ETML-ES-SLO/PRJ_2113_D-sElectronique/doc/Schéma bloc.docx

SPI / CONFIG

3.3V

INT1

3.3V

Maintien d’alimentation

Microcontrôleur

3.3V

V pile

Alimentation

Accéléromètre

Régulateur / élévateur
