ETML-ES-SLO/PRJ_2113_D-sElectronique/doc/PV/PV_N2_MaximeColloud_14_10_2021.docx

Procès-verbal du 14.10.2021

Présents

- M. Serge Castoldi
- M. Maxime Colloud

État des lieux

- Schéma et PCB presque terminé (modifications à faire)
- Composants presque choisi (changements à faire)

Problèmes rencontrés

- Self sous dimensionnée
- Reconfiguration de l’accéléromètre non présente si pile retirée ou vide

Solutions proposées

- Ajout d’un bouton pour reconfigurer l’accéléromètre en cas de pile retirée ou vide

Décisions prises

- Changement inductance L1 et C1
- Ajout du signal interrupt sur le microcontrôleur
- Modification de la taille du PCB avec une largeur plus grande que spécifié dans le cahier des

Charge pour une simplification du boitier et hauteur plus petite

Suite du projet / objectifs - jusqu’au jeudi 21.10.2021

- Modifier le schéma, PCB
- Créer un boitier
- Tester avec le kit micro MM la configuration d’un chip MM
- Commander le PCB et composants

Prochaine réunion:

21.10.2021 à 13h

Destinataires de ce PV

- Grégoire Rossier → Doyen ES
- Serge Castoldi → Enseignant ES

Lausanne le 14.10.2021

Maxime Colloud

PV_N2_MaximeColloud_14_10_2021.docx 14.10.2021 - page 2 / 2

Ecole supérieure, école des métiers Lausanne Version 2.2 Rue de Sébeillon 12 du 02.09.2021 CH-1004 Lausanne www.etml-es.ch PV_N2_MaximeColloud_14_10_2021.docx | 1 / 2 |

ETML-ES PV de séance diplôme
