ETML-ES-SLO/PRJ_2113_D-sElectronique/doc/PDF/2113_Suivi d'avancement.pdf

## Projet 2113 Dé électronique Maxime Colloud

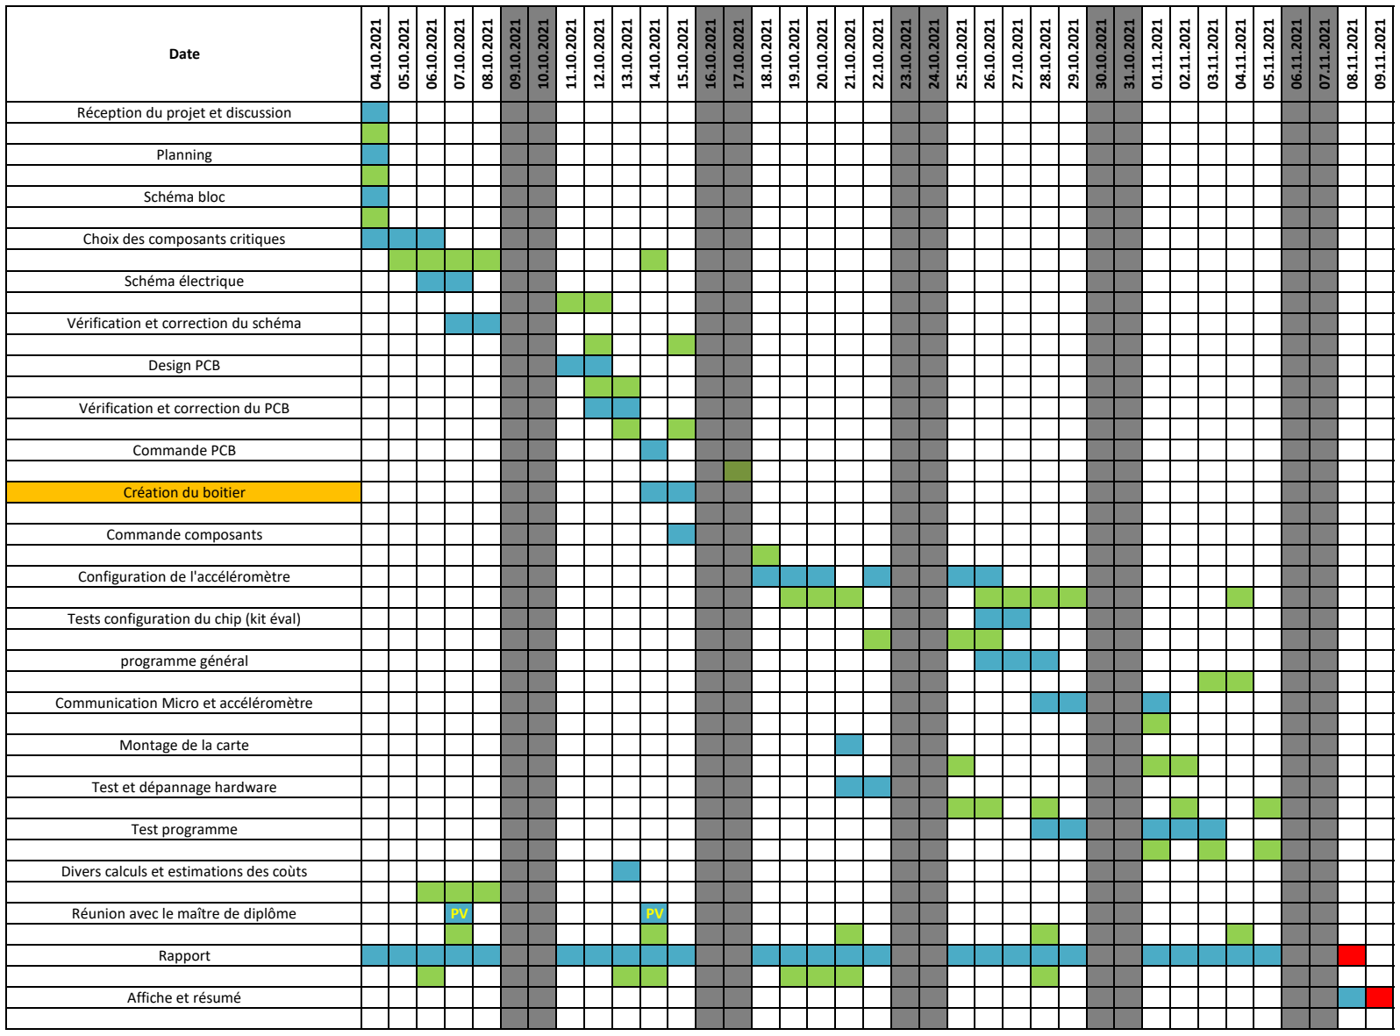
[picture p47: figure]
Réception du projet et discussion; Planning; Schéma bloc; Choix des composants critiques; Schéma électrique; Vérification et correction du schéma; Design PCB; Vérification et correction du PCB; Commande PCB; Création du boitier; Commande composants; Configuration de l'accéléromètre; Tests configuration du chip (kit éval); programme général; Communication Micro et accéléromètre; Montage de la carte; Test et dépannage hardware; Test programme; Divers calculs et estimations des coùts; Réunion avec le maître de diplôme; Rapport; Affiche et résumé; Date

# : deadline du projet ⁰⁸.10.2021 09.10.2021
