ETML-ES-SLO/PRJ_2113_D-sElectronique/doc/PDF/DeElectroniqueC.pdf

1 #include "DeElectronique.h" 2

### 3 void NONUM (void)

4 {
5 LED0 = 0;
6 LED1 = 0;
7 LED2 = 0;
8 LED3 = 0;
9 LED4 = 0;
10 LED5 = 0;
11 LED6 = 0;
12 }

### 13 void NUM1 (void)

14 {
15 LED3 = 1;
16 }

### 17 void NUM2 (void)

18 {
19 LED0 = 1;
20 LED6 = 1;
21 }

### 22 void NUM3 (void)

23 {
24 LED0 = 1;
25 LED3 = 1;
26 LED6 = 1;
27 }

### 28 void NUM4 (void)

29 {
30 LED0 = 1;
31 LED2 = 1;
32 LED4 = 1;
33 LED6 = 1;
34 }

### 35 void NUM5 (void)

36 {
37 LED0 = 1;
38 LED2 = 1;
39 LED3 = 1;
40 LED4 = 1;
41 LED6 = 1;
42 }

### 43 void NUM6 (void)

44 {
45 LED0 = 1;
46 LED1 = 1;
47 LED2 = 1;
48 LED4 = 1;
49 LED5 = 1;
50 LED6 = 1;
51 }
52

### 53 void RandomNum (int Number)

54 {
55 uint8_t EntierNumber;
56
57 EntierNumber = Number %6; 58

### 59 switch (EntierNumber)

60 {

### 61 case 0 :

62 NUM1();
63 break;

### 64 case 1 :

65 NUM2();
66 break;

### 67 case 2 :

68 NUM3();
69 break;

### 70 case 3 :

71 NUM4();
72 break;

### 73 case 4 :

74 NUM5();
75 break | ;
76 case | 5 :
77 NUM6();
78 break | ;
79 default | :
80 break | ;
81 | }
82 | }
