ETML-ES-SLO/PRJ_2113_D-sElectronique/doc/PDF/DeElectroniqueH.pdf

1 /*
2 | * File: | DeElectronique.h
3 * Author: maxcolloud
4 *
5 * Created on November 3, 2021, 1:35 PM 6 */
7
8 #include "xc.h"
9 #include "Accelerometre.h" 10
11 #ifndef DEELECTRONIQUE_H 12 #define DEELECTRONIQUE_H 13
14
15 #ifdef __cplusplus

### 16 extern "C" {

17 #endif
18
19 #define INT_SHAKE PORTBbits.RB12 20
21 #define LED0 LATAbits.LATA0
22 #define LED1 LATAbits.LATA1
23 #define LED2 LATAbits.LATA2 24 #define LED3 LATBbits.LATB2 25 #define LED4 LATAbits.LATA3 26 #define LED5 LATBbits.LATB4 27 #define LED6 LATAbits.LATA4 28
29 #define HOLD LATBbits.LATB13 30
31 // Fonctions
32 void NONUM (void);
33 void NUM1 (void);
34 void NUM2 (void);
35 void NUM3 (void);
36 void NUM4 (void);
37 void NUM5 (void);
38 void NUM6 (void);
39 void RandomNum (int Number); 40
41 #ifdef __cplusplus
42 }
43 #endif
44
45 #endif /* DEELECTRONIQUE_H */ 46
47
