ETML-ES-SLO/PRJ_2113_D-sElectronique/doc/PDF/Planning.pdf

## Projet 2113 Dé électronique Maxime Colloud

10.10.2021

11.10.2021

12.10.2021

13.10.2021

14.10.2021

15.10.2021

16.10.2021

17.10.2021

18.10.2021

19.10.2021

20.10.2021

21.10.2021

22.10.2021

23.10.2021

24.10.2021

25.10.2021

26.10.2021

27.10.2021

28.10.2021
29.10.2021

30.10.2021

31.10.2021

01.11.2021

02.11.2021

03.11.2021

04.11.2021

05.11.2021

06.11.2021

07.11.2021

08.11.2021

09.11.2021

Date

Réception du projet et discussion Planning
Schéma bloc
Choix des composants critiques Schéma électrique
Vérification et correction du schéma | : deadline du projet ⁰⁸.10.2021 | | 09.10.2021

Design PCB
Vérification et correction du PCB Commande PCB
Création du boitier
Commande composants
Configuration de l'accéléromètre Tests configuration du chip (kit éval) programme général
Communication Micro et accéléromètre Montage de la carte
Test et dépannage hardware
Test programme
Divers calculs et estimations des coùts
Réunion avec le maître de diplôme | | PV | | PV
Rapport
Affiche et résumé

04.10.2021

05.10.2021

06.10.2021

07.10.2021
