ETML-ES-SLO/PRJ_2113_D-sElectronique/doc/PDF/PV_N1_MaximeColloud_07_10_2021.pdf

ETML⁻ES
PV de séance | diplôme
Ecole supérieure, école des métiers Lausanne | Version 2.2
Rue de Sébeillon 12 | du 02.09.2021
CH-1004 Lausanne | www.etml-es.ch
Procès verbal TYPE_v2-2.docx | | 1 / 2 |

## Procès-verbal du 07.10.2021

Présents

- M. Sege Castoldi
- M. Maxime Colloud

État des lieux

- Choix d’une variante de montage (PIC32MM, 1 pile alkaline, 1 convertisseur step-up)

Problèmes rencontrés

- Disponibilité des composants faible
- Step-up présélectionné non adapté aux faibles consommations.

Solutions proposées

- Ajout d’un système de sécurité d’alimentation inverse

Décisions prises

- Utilisation du PICMM 20 pin
- utilisation de l’accéléromètre MC3419
- choix d’un convertisseur step-up en basse consommation.
- Utilisation d’un mosfet canal-p pour la protection d’alimentation inverse

Suite du projet / objectifs - jusqu’au jeudi 14 août

- Choix des derniers composants, Schéma, Design PCB.

Prochaine réunion:

14.10.2021 à 13h

ETML⁻ES

Procès verbal TYPE_v2-2.docx | 07.10.2021 - page 2 / 2

Destinataires de ce PV

- Grégoire Rossier → Doyen ES
- Serge Castoldi → Enseignant ES

Lausanne le 07.10.2021

Maxime Colloud
