ETML-ES-SLO/PRJ_2113_D-sElectronique/doc/PDF/PV_N3_MaximeColloud_21_10_2021.pdf

ETML⁻ES
PV de séance | diplôme
Ecole supérieure, école des métiers Lausanne | Version 2.2
Rue de Sébeillon 12 | du 02.09.2021
CH-1004 Lausanne | www.etml-es.ch
PV_N2_MaximeColloud_21_10_2021.docx | | 1 / 2 |

## Procès-verbal du 21.10.2021

Présents

- M. Serge Castoldi
- M. Maxime Colloud

État des lieux

- PCB commandé et reçu
- Composants reçu
- Premier de configuration pic32MM fait sur le kitMM

Problèmes rencontrés

- Aucun

Solutions proposées

- Le cahier des charges stipule que le chiffre doit être affiché quand le dé est reposé à l’horizontal. N’étant pas pratique pour l’utilisateur, il faudrait modifier pour afficher lors d’un arrêt de mouvement.

Décisions prises

- Afficher le chiffre lors d’un arrêt de mouvement.

Suite du projet / objectifs - jusqu’au jeudi 21.10.2021

- Montage PCB
- Programmation

Prochaine réunion:

28.10.2021 à 13h

ETML⁻ES

PV_N2_MaximeColloud_21_10_2021.docx | 25.10.2021 - page 2 / 2

Destinataires de ce PV

- Grégoire Rossier → Doyen ES
- Serge Castoldi → Enseignant ES

Lausanne le 25.10.2021

Maxime Colloud
