ETML-ES-SLO/PRJ_2113_D-sElectronique/doc/Affiche PROJET SLO_v1.pdf

Maxime Colloud
TECHNICIEN-NE ES EN GÉNIE ÉLECTRIQUE / 2020-2021

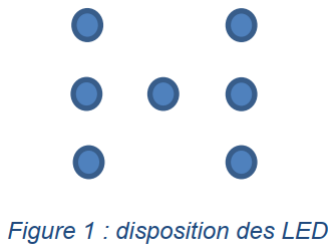
[picture p51: figure]

### www.etml-es.ch

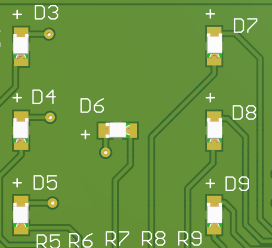
[picture p52: figure]
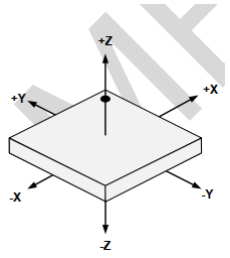
[picture p53: figure]

rue de Sébeillon 12, 1004 Lausanne | ETML

DeElectronique

Le dé peut détecter les actions de secouement et se réveiller par cette même action. Par problème de dimensionnement de l’élévateur, le dé ne fonctionne pas à l’utilisation d’une pile. En debug, il peut générer un chiffre aléatoire lors d’un secouement détecté.

Ce projet est un dé électronique destiné à être distribué aux visiteurs des portes ouvertes de l’ES. Le dé a pour objectif d’afficher un chiffre lorsqu’il détecte une action de secouement. Le chiffre s’affichera pour une durée de 10sec. L’appareil utilise une pile AA pour son fonctionnement et possède une grande autonomie.

## Affichage des chiffres sous la forme d’un dé à lancer

## Fonctionnement par une pile AA. Simple d’utilisation et avec une bonne autonomie
