ETML-ES-SLO/PRJ_2113_D-sElectronique/doc/PDF/mainc.pdf

1 /**

### 2 Generated main.c file from MPLAB Code Configurator

3
4 @Company
5 Microchip Technology Inc.
6
7 @File Name

### 8 main.c

9
10 @Summary
11 This is the generated main.c using PIC24 / dsPIC33 / PIC32MM MCUs.
12
13 @Description

### 14 This source file provides main entry point for system intialization and

application code development.

### 15 Generation Information : 16 Product Revision : PIC24 / dsPIC33 / PIC32MM MCUs - 1.75.1

17 | Device | : PIC32MM0064GPL020

### 18 The generated drivers are tested against the following:

19 | Compiler | : XC16 v1.35
20 | MPLAB | : MPLAB X v5.05
21 */
22
23 /*
24 (c) 2016 Microchip Technology Inc. and its subsidiaries. You may use this 25 software and any derivatives exclusively with Microchip products.
26

27 THIS SOFTWARE IS SUPPLIED BY MICROCHIP "AS IS". NO WARRANTIES, WHETHER 28 EXPRESS, IMPLIED OR STATUTORY, APPLY TO THIS SOFTWARE, INCLUDING ANY IMPLIED 29 WARRANTIES OF NON-INFRINGEMENT, MERCHANTABILITY, AND FITNESS FOR A 30 PARTICULAR PURPOSE, OR ITS INTERACTION WITH MICROCHIP PRODUCTS, COMBINATION

31 WITH ANY OTHER PRODUCTS, OR USE IN ANY APPLICATION.
32
33 IN NO EVENT WILL MICROCHIP BE LIABLE FOR ANY INDIRECT, SPECIAL, PUNITIVE,

34 INCIDENTAL OR CONSEQUENTIAL LOSS, DAMAGE, COST OR EXPENSE OF ANY KIND 35 WHATSOEVER RELATED TO THE SOFTWARE, HOWEVER CAUSED, EVEN IF MICROCHIP HAS 36 BEEN ADVISED OF THE POSSIBILITY OR THE DAMAGES ARE FORESEEABLE. TO THE 37 FULLEST EXTENT ALLOWED BY LAW, MICROCHIP'S TOTAL LIABILITY ON ALL CLAIMS IN

38 ANY WAY RELATED TO THIS SOFTWARE WILL NOT EXCEED THE AMOUNT OF FEES, IF ANY, 39 THAT YOU HAVE PAID DIRECTLY TO MICROCHIP FOR THIS SOFTWARE.
40

### 41 MICROCHIP PROVIDES THIS SOFTWARE CONDITIONALLY UPON YOUR ACCEPTANCE OF THESE

42 TERMS.
43 */
44
45 /**

### 46 Section: Included Files

47 */
48
49 #include "mcc_generated_files/system.h"
50 #include "mcc_generated_files/spi1.h"
51 #include "mcc_generated_files/pin_manager.h" 52 #include "Accelerometre.h"
53 #include "DeElectronique.h"
54 #include "mcc_generated_files/tmr1.h"
55 /*

### 56 Main application

57 */

### 58 int main(void)

59 {
60 // initialize the device
61 SYSTEM_Initialize();
62 | HOLD = 1; | //assure maintien alim.
63
64 MC3419_start();
65
66 | // | if (!INT_SHAKE)
67 | // | {
68 | // | MC3419_start();
69 | // | HOLD = 0;
70 | // | while(1);
71 | // | }
72 | // | uint8_t test;

73 | // int seed;
74 while (1)
75 {
76 | // test = MC3419_ReadStatusRegister();
77 | // if (test == SHAKE_INT)
78 | // {
79 | // seed = ReadRegister8(addr_Xout_Ex_L);
80 | // seed = seed + ReadRegister8(addr_Xout_Ex_H);
81 | // seed = seed + ReadRegister8(addr_Yout_Ex_L);
82 | // seed = seed + ReadRegister8(addr_Yout_Ex_H);
83 | // seed = seed + ReadRegister8(addr_Zout_Ex_L);
84 | // seed = seed + ReadRegister8(addr_Zout_Ex_H);
85 | // srand (seed);
86 | // seed = rand();
87 | // RandomNum (seed);
88 TMR1_Start();
89 | // }
90 }
91 return 1;
92 }
93 /**
94 End of File
95 */
