ETML-ES-SLO/PRJ_2113_D-sElectronique/soft/2113_DeElectronique_V2.X/latex/main_8c__incl.pdf

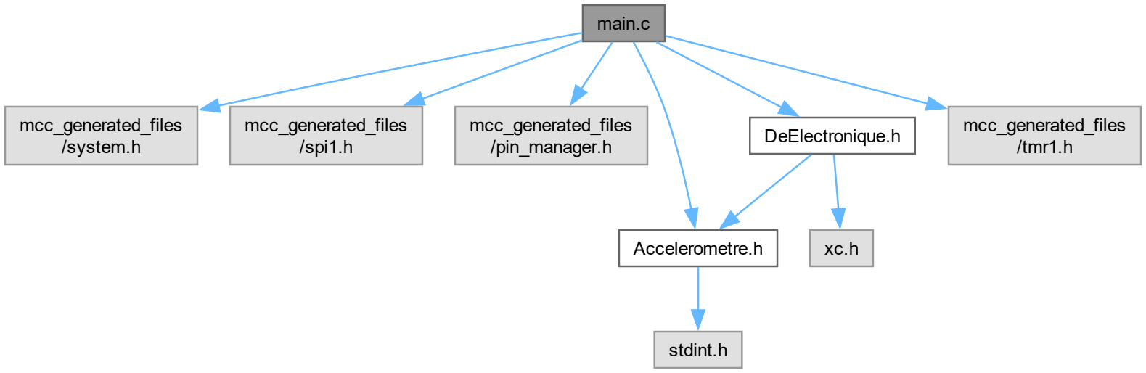
[picture p54: figure]
main.c; mcc_generated_files /system.h; mcc_generated_files /spi1.h; mcc_generated_files /pin_manager.h; Accelerometre.h; DeElectronique.h; mcc_generated_files; /tmr1.h; stdint.h
