ETML-ES-SLO/PRJ_2113_D-sElectronique/soft/2113_DeElectronique_V3.X/code2flow/soft_v3.png

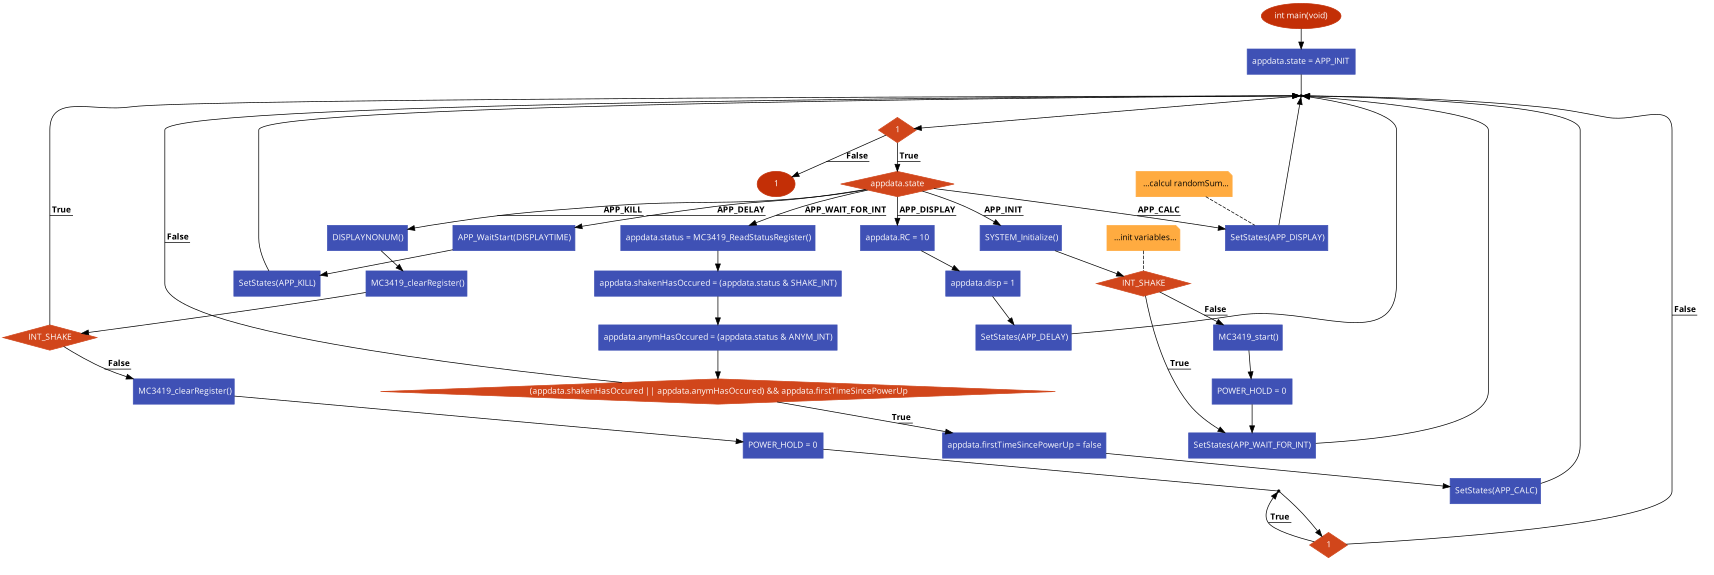
soft/2113_DeElectronique_V3.X/code2flow/soft_v3.png
