ETML-ES-SLO/PRJ_2113_D-sElectronique/soft/2113_DeElectronique_V3.X/code2flow/State_Delay.png

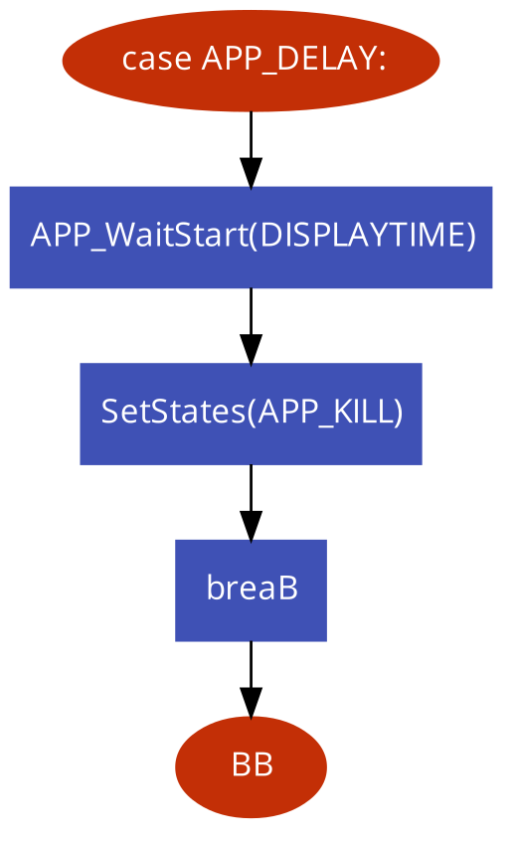
soft/2113_DeElectronique_V3.X/code2flow/State_Delay.png
