ETML-ES-SLO/PRJ_2113_D-sElectronique/soft/2113_DeElectronique_V3.X/html/_accelerometre_8c_a3add481cd74b85a6100f501bc62df540_cgraph.png

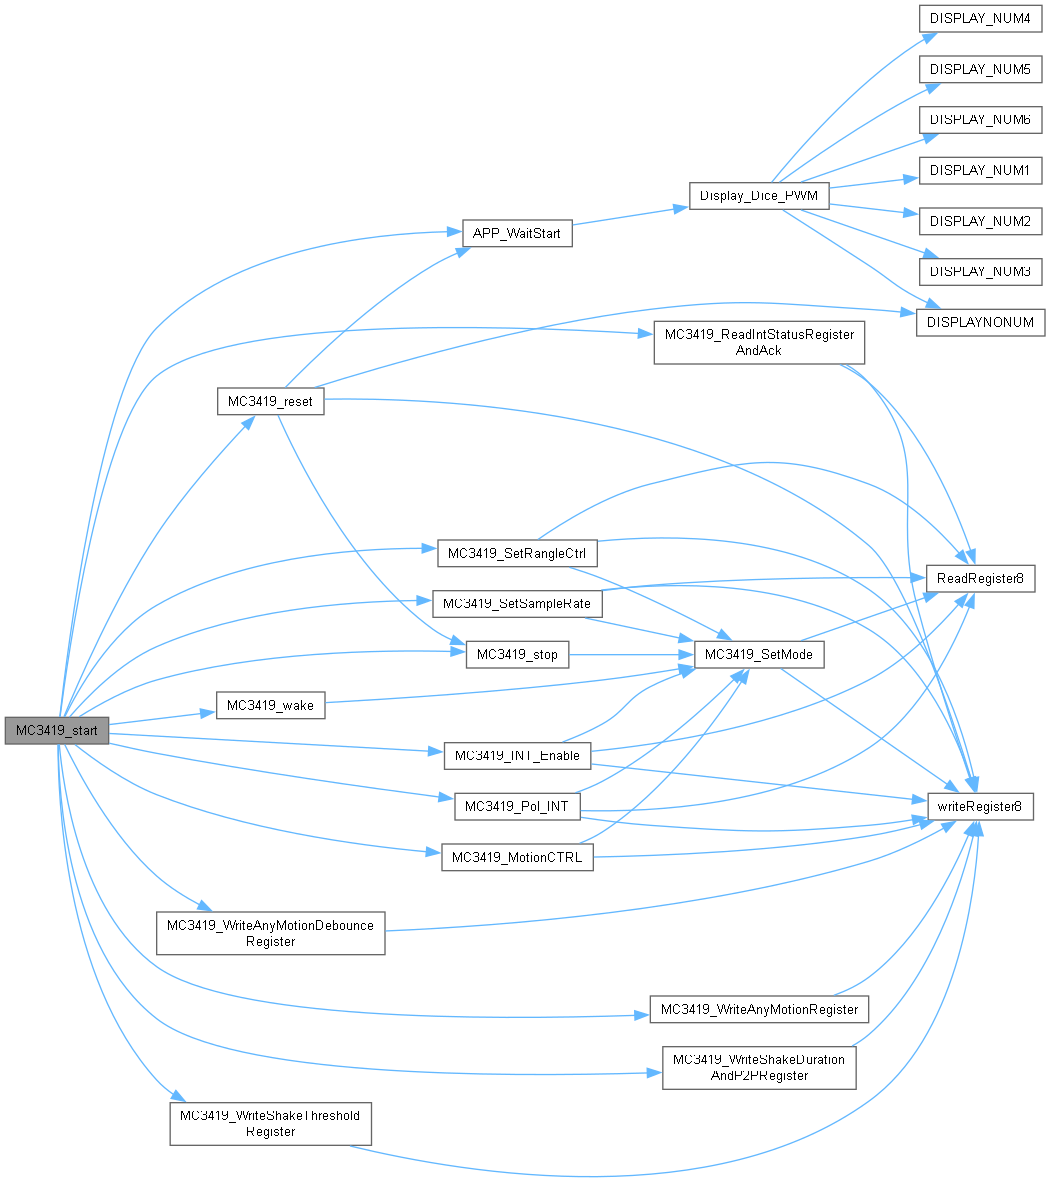
soft/2113_DeElectronique_V3.X/html/_accelerometre_8c_a3add481cd74b85a6100f501bc62df540_cgraph.png
