ETML-ES-SLO/PRJ_2113_D-sElectronique/soft/2113_DeElectronique_V3.X/html/_accelerometre_8c_a9ae57db275809bc093fb879e023b3c5e_icgraph.png

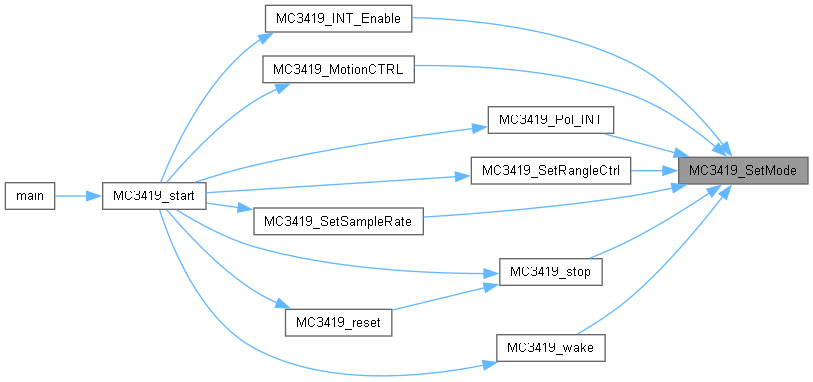
soft/2113_DeElectronique_V3.X/html/_accelerometre_8c_a9ae57db275809bc093fb879e023b3c5e_icgraph.png
