ETML-ES-SLO/PRJ_2113_D-sElectronique/soft/2113_DeElectronique_V3.X/html/_accelerometre_8c_a45a6c20144b882f4067231cc340b942c_icgraph.png

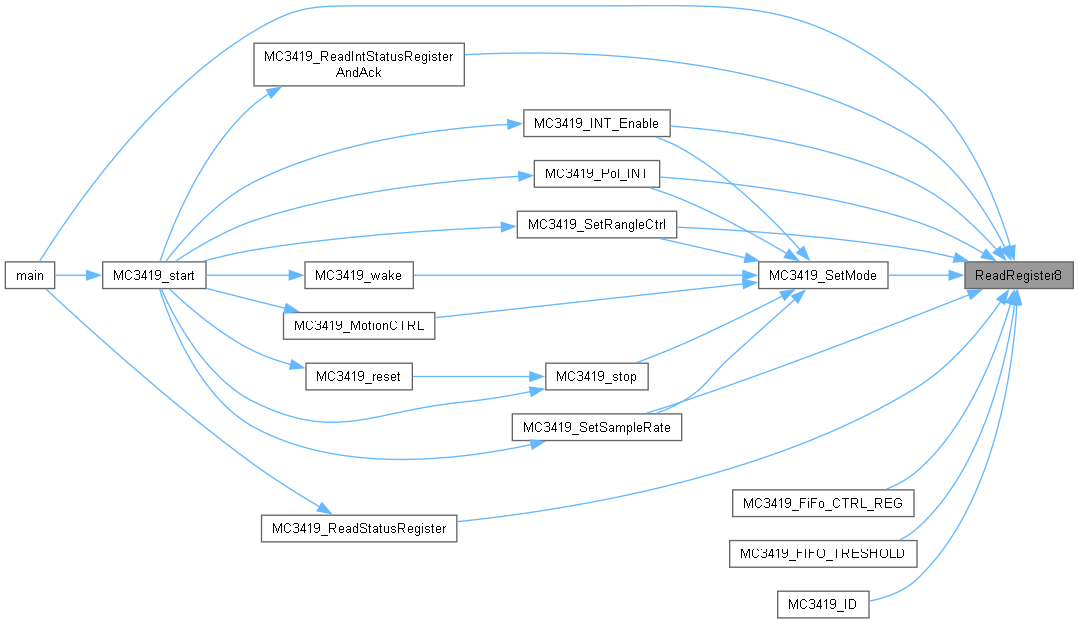
soft/2113_DeElectronique_V3.X/html/_accelerometre_8c_a45a6c20144b882f4067231cc340b942c_icgraph.png
