ETML-ES-SLO/PRJ_2113_D-sElectronique/soft/2113_DeElectronique_V3.X/html/_accelerometre_8c_a85c42d11f42919bc5139bb178d08827a_cgraph.png

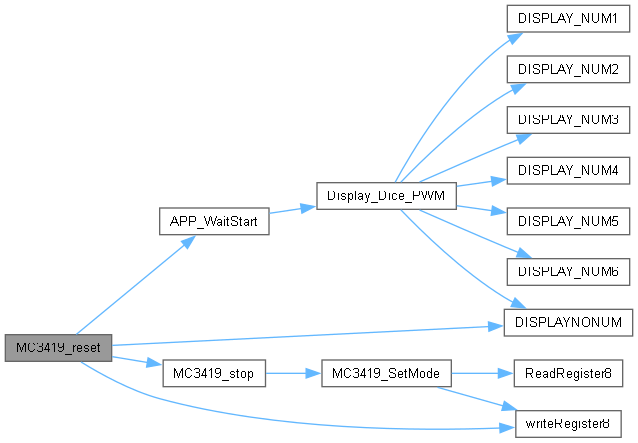
soft/2113_DeElectronique_V3.X/html/_accelerometre_8c_a85c42d11f42919bc5139bb178d08827a_cgraph.png
