ETML-ES-SLO/PRJ_2113_D-sElectronique/soft/2113_DeElectronique_V3.X/html/_accelerometre_8c_a43618e36fd841e9db9fc0463f6c5d129_icgraph.png

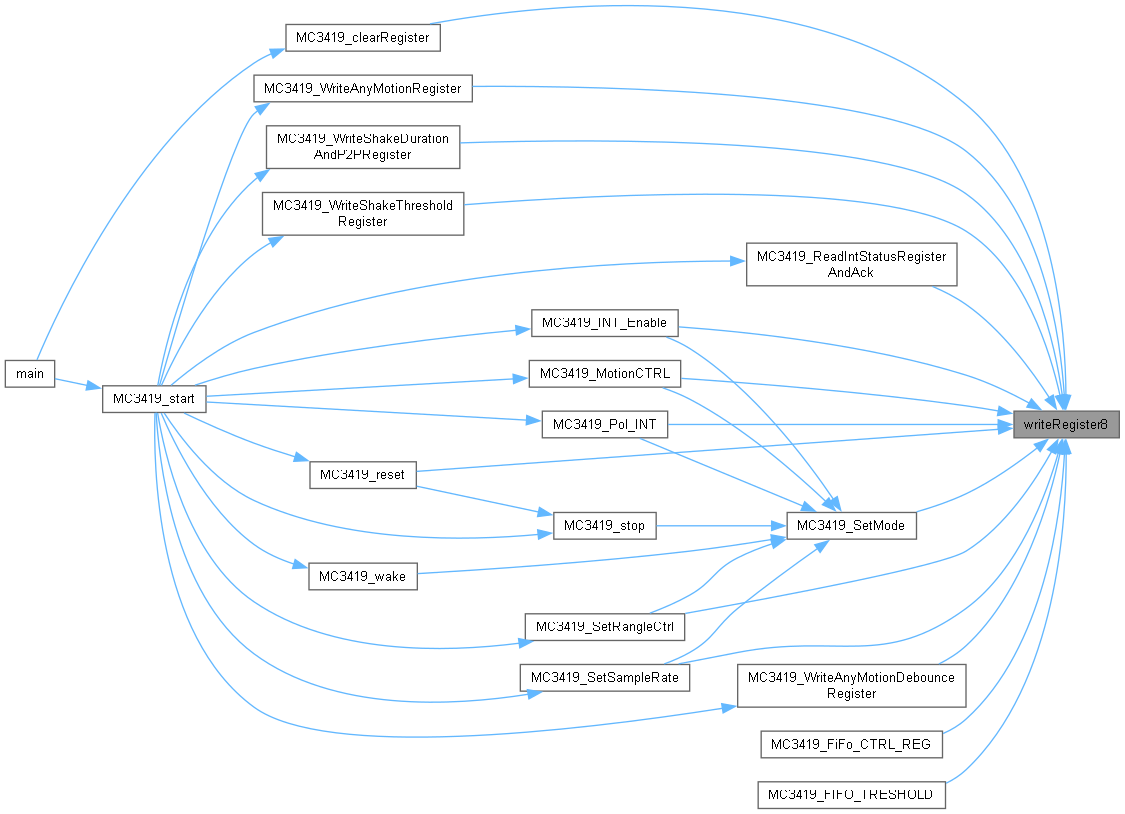
soft/2113_DeElectronique_V3.X/html/_accelerometre_8c_a43618e36fd841e9db9fc0463f6c5d129_icgraph.png
