ETML-ES-SLO/PRJ_2113_D-sElectronique/soft/2113_DeElectronique_V3.X/html/_de_electronique_8c_a19aa8cfabaac6b4b667a1aa5af004484_cgraph.png

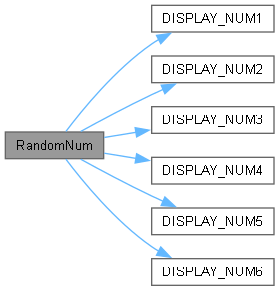
soft/2113_DeElectronique_V3.X/html/_de_electronique_8c_a19aa8cfabaac6b4b667a1aa5af004484_cgraph.png
