ETML-ES-SLO/PRJ_2113_D-sElectronique/soft/2113_DeElectronique_V3.X/html/_de_electronique_8c_a742bce1c2f22b159570e071b6b4c855d_cgraph.png

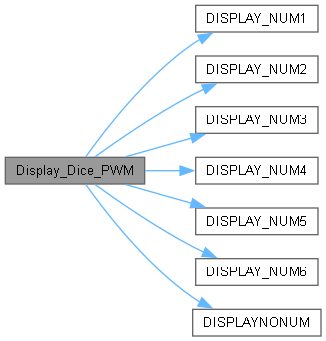
soft/2113_DeElectronique_V3.X/html/_de_electronique_8c_a742bce1c2f22b159570e071b6b4c855d_cgraph.png
