ETML-ES-SLO/PRJ_2113_D-sElectronique/soft/2113_DeElectronique_V3.X/html/_de_electronique_8h__incl.png

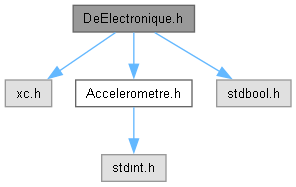
soft/2113_DeElectronique_V3.X/html/_de_electronique_8h__incl.png
