ETML-ES-SLO/PRJ_2113_D-sElectronique/soft/2113_DeElectronique_V3.X/html/_mc32_delays_8c__incl.png

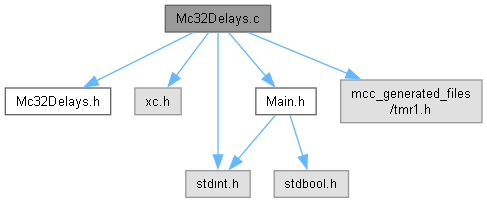
soft/2113_DeElectronique_V3.X/html/_mc32_delays_8c__incl.png
