ETML-ES-SLO/PRJ_2113_D-sElectronique/soft/2113_DeElectronique_V3.X/latex/main_8c__incl.pdf

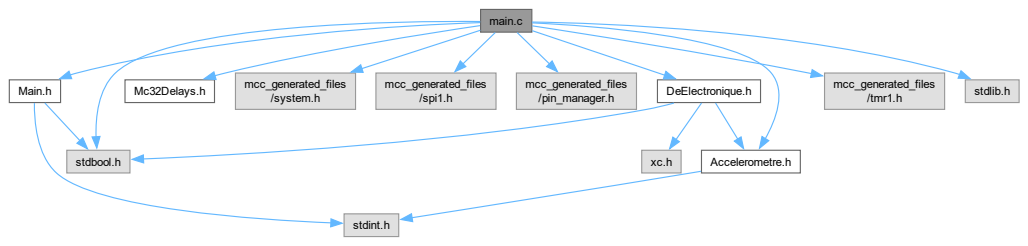
[picture p81: page 1]
main.c; Main.h; stdbool.h; Mc32Delays.h; mcc_generated_files; /system.h; mcc_generated_files /spi1.h; mcc_generated_files /pin_manager.h; Accelerometre.h; DeElectronique.h; /tmr1.h; stdlib.h; stdint.h
