ETML-ES-SLO/PRJ_2113_D-sElectronique/soft/2113_DeElectronique_V3.X/latex/main_8c_a840291bc02cba5474a4cb46a9b9566fe_cgraph.pdf

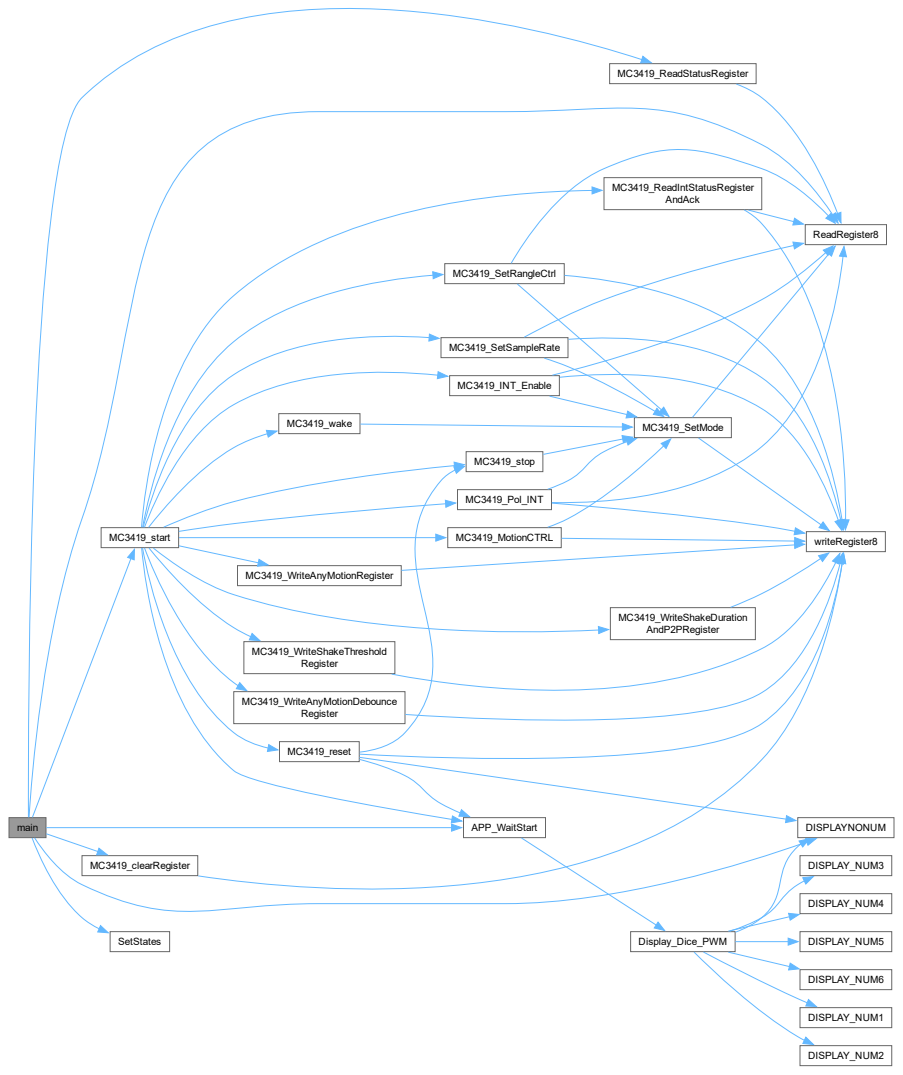
[picture p84: page 1]
main; APP_WaitStart; DISPLAYNONUM; MC3419_clearRegister; MC3419_ReadStatusRegister; ReadRegister8; MC3419_start; SetStates; Display_Dice_PWM; DISPLAY_NUM1; DISPLAY_NUM2; DISPLAY_NUM3; DISPLAY_NUM4; DISPLAY_NUM5; DISPLAY_NUM6; writeRegister8; MC3419_INT_Enable; MC3419_MotionCTRL; MC3419_Pol_INT; MC3419_ReadIntStatusRegister AndAck; MC3419_reset; MC3419_stop; MC3419_SetRangleCtrl; MC3419_SetSampleRate; MC3419_wake; MC3419_WriteAnyMotionDebounce Register; MC3419_WriteAnyMotionRegister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
