ETML-ES-SLO/PRJ_2113_D-sElectronique/soft/2113_DeElectronique_V2.X/latex/main_8c_a840291bc02cba5474a4cb46a9b9566fe_cgraph.pdf

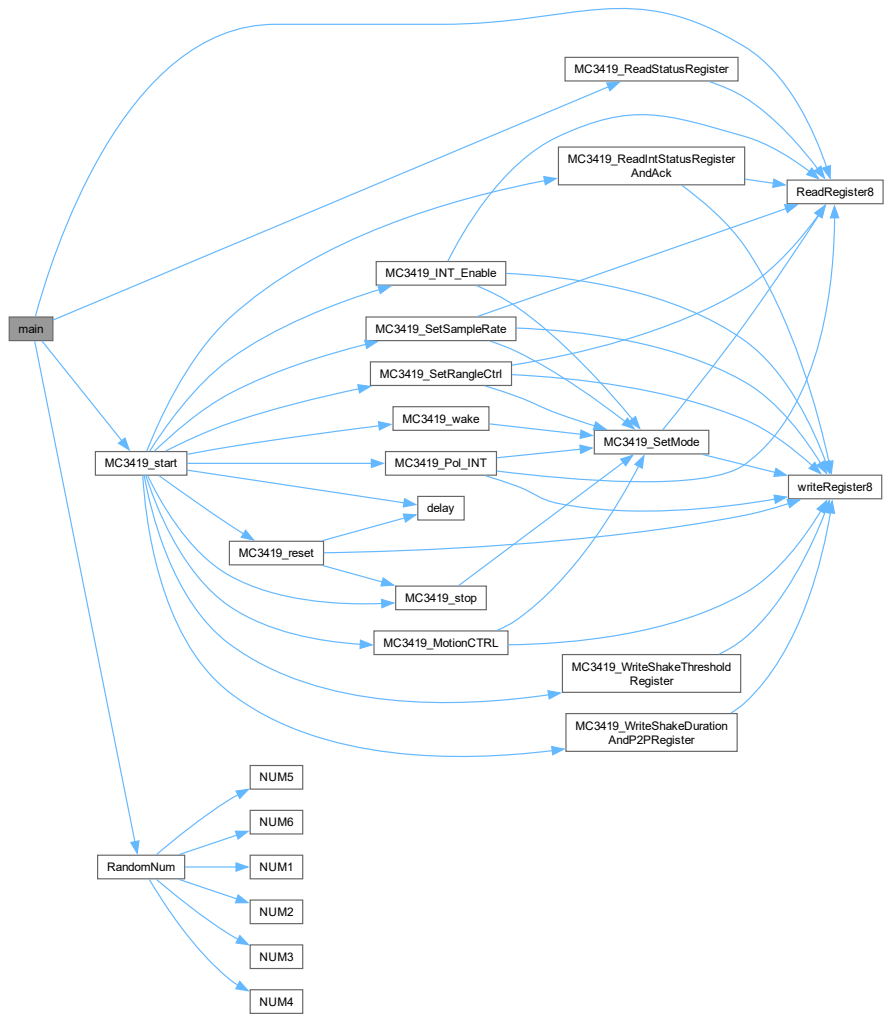
[picture p85: page 1]
main; MC3419_ReadStatusRegister; ReadRegister8; MC3419_start; RandomNum; delay; MC3419_INT_Enable; MC3419_MotionCTRL; MC3419_Pol_INT; MC3419_ReadIntStatusRegister AndAck; MC3419_reset; MC3419_stop; MC3419_SetRangleCtrl; MC3419_SetSampleRate; MC3419_wake; MC3419_WriteShakeDuration AndP2PRegister; MC3419_WriteShakeThreshold Register; MC3419_SetMode; writeRegister8; NUM1; NUM2; NUM3; NUM4; NUM5; NUM6
